Mook-Tetove/Roundness-measurement-algorithm/Roundness measuring instrument/型材/圆度-铝型材-2020-50.SLDPRT

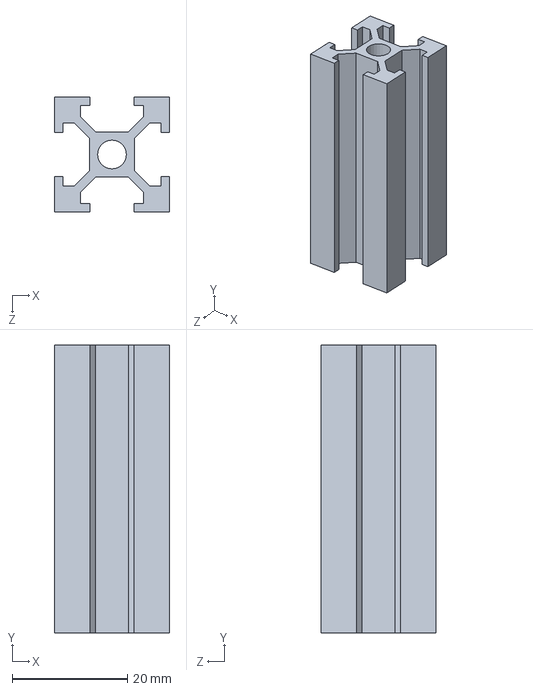
[picture p15: CAD file, 2025-03-15]
Roundness measuring instrument/型材/圆度-铝型材-2020-50.SLDPRT
20.0 x 50.0 x 20.0 mm
