Mook-Tetove/Roundness-measurement-algorithm/Roundness measuring instrument/电子/圆度-标准件-50减速比减速箱.SLDPRT

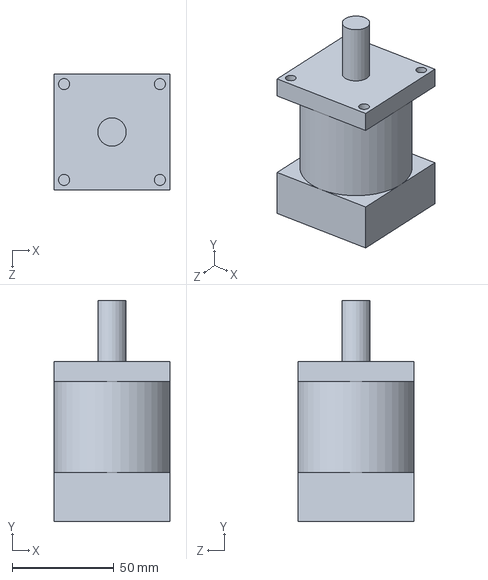
[picture p16: CAD file, 2025-03-15]
Roundness measuring instrument/电子/圆度-标准件-50减速比减速箱.SLDPRT
57.0 x 108.8 x 57.0 mm
