Mook-Tetove/Roundness-measurement-algorithm/Roundness measuring instrument/五金/圆度-标准件-57步进电机减速箱支架.SLDPRT

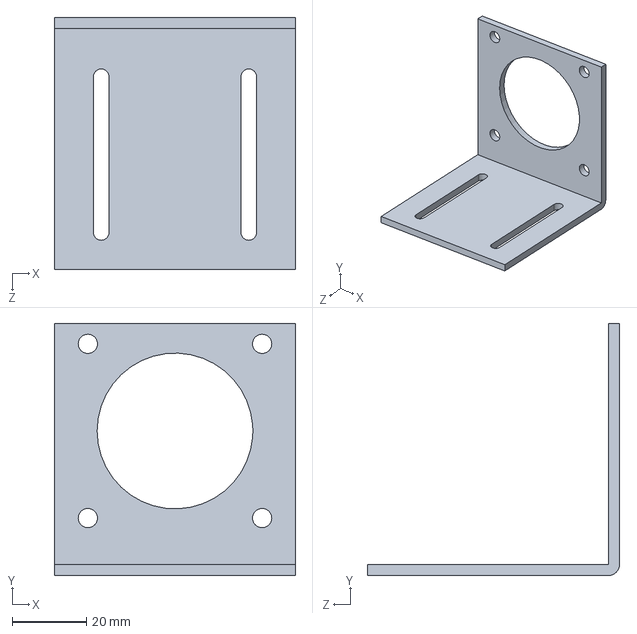
[picture p17: CAD file, 2025-03-15]
Roundness measuring instrument/五金/圆度-标准件-57步进电机减速箱支架.SLDPRT
65.0 x 68.0 x 68.0 mm
