Mook-Tetove/Roundness-measurement-algorithm/Roundness measuring instrument/型材/圆度-铝型材-4040-500.SLDPRT

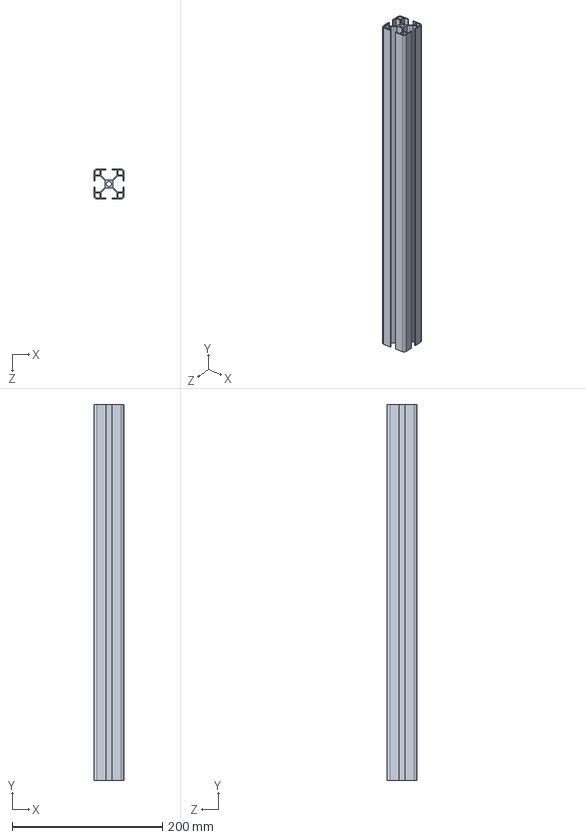
[picture p18: CAD file, 2025-03-15]
Roundness measuring instrument/型材/圆度-铝型材-4040-500.SLDPRT
40.0 x 500.0 x 40.0 mm
