Mook-Tetove/Roundness-measurement-algorithm/Roundness measuring instrument/五金/圆度-梅花联轴器-14-30-35.SLDPRT

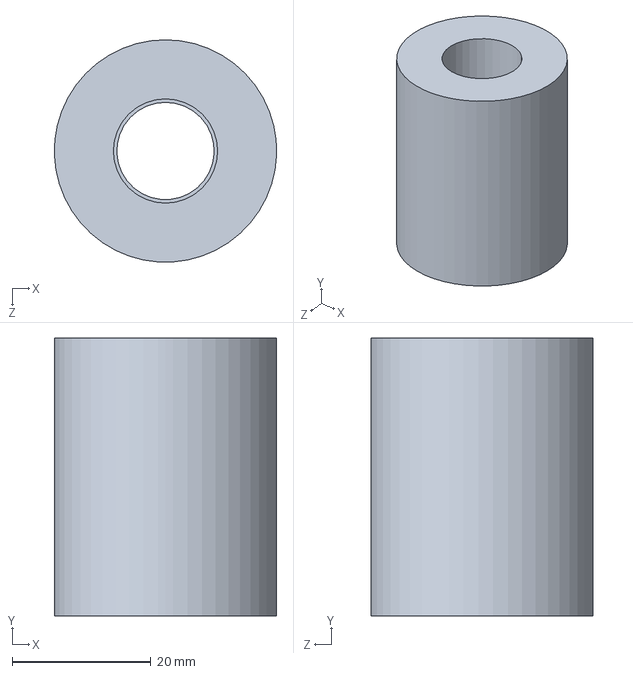
[picture p19: CAD file, 2025-03-15]
Roundness measuring instrument/五金/圆度-梅花联轴器-14-30-35.SLDPRT
32.0 x 40.0 x 32.0 mm
