Mook-Tetove/Roundness-measurement-algorithm/Roundness measuring instrument/型材/圆度-铝型材-4040-200.SLDPRT

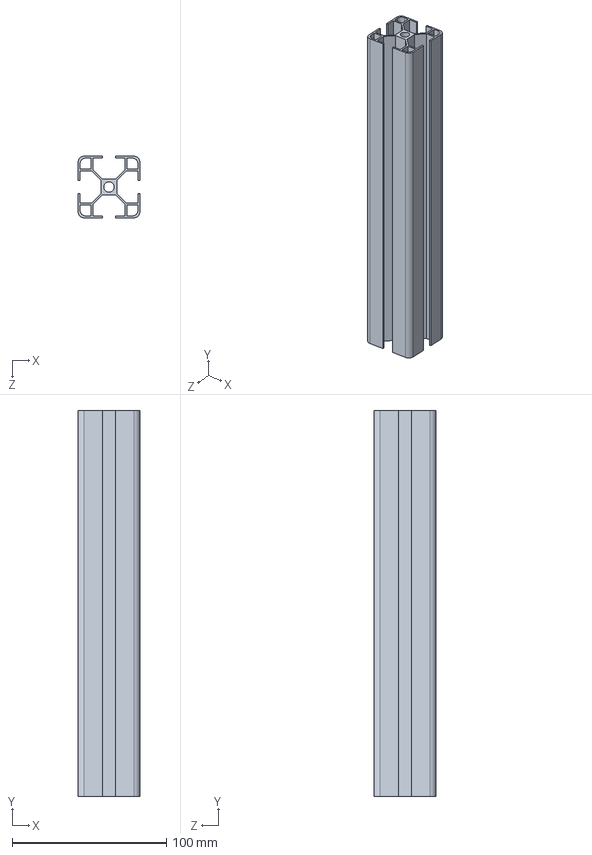
[picture p20: CAD file, 2025-03-15]
Roundness measuring instrument/型材/圆度-铝型材-4040-200.SLDPRT
40.0 x 250.0 x 40.0 mm
