Mook-Tetove/Roundness-measurement-algorithm/Roundness measuring instrument/五金/圆度-钢杆-15-200.SLDPRT

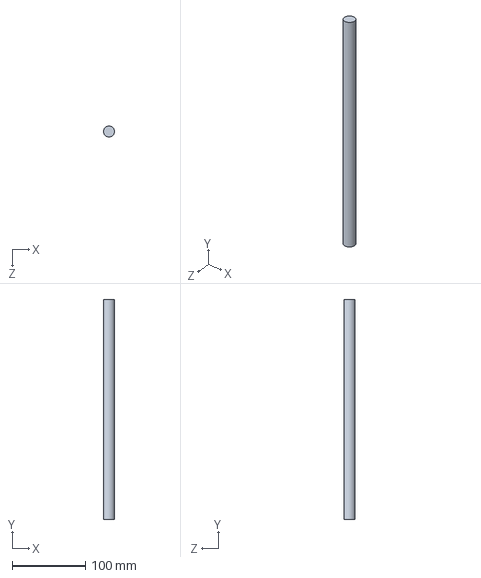
[picture p21: CAD file, 2025-03-15]
Roundness measuring instrument/五金/圆度-钢杆-15-200.SLDPRT
15.0 x 300.0 x 15.0 mm
