Mook-Tetove/Roundness-measurement-algorithm/Roundness measuring instrument/型材/圆度-铝型材-2020-100.SLDPRT

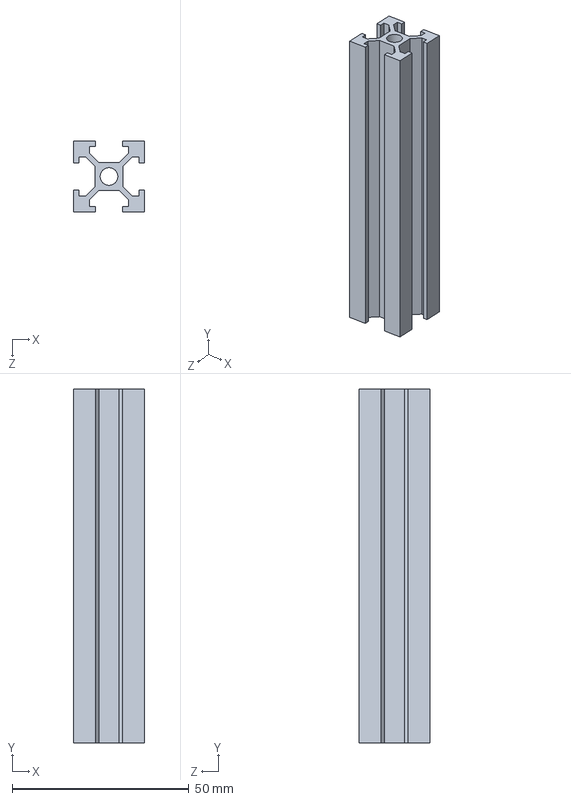
[picture p22: CAD file, 2025-03-15]
Roundness measuring instrument/型材/圆度-铝型材-2020-100.SLDPRT
20.0 x 100.0 x 20.0 mm
